nima34366/alarm_clock/microproducts/key_input/simulation/simulation.ino

#include <Keypad.h>

const int ROW_NUM = 3; //four rows
const int COLUMN_NUM = 3; //four columns

char keys[ROW_NUM][COLUMN_NUM] = {
  {'1', '2', '3'},
  {'4', '5', '6'},
  {'7', '8', '9'}
};

byte pin_rows[ROW_NUM] = {A0, A1, A2}; //connect to the row pinouts of the keypad
byte pin_column[COLUMN_NUM] = {A3, A4, A5}; //connect to the column pinouts of the keypad

Keypad keypad = Keypad( makeKeymap(keys), pin_rows, pin_column, ROW_NUM, COLUMN_NUM );

void setup()
{
  for (int i = 2; i <= 10; i++)
  {
    pinMode(i, OUTPUT);
  }
}

void loop()
{
  char key = keypad.getKey();
  if (key != NO_KEY )
  {
    for (int k = 49; k <= key; k++)
    {
      digitalWrite(k - 47, HIGH) ;
    }
    delay(1000);

    for (int p = 2; p <= 10; p++)
    {
      digitalWrite(p, LOW);
    }
  }
}
